erikvanzijst/dotmatrix/media/arduino_tetris.jpg

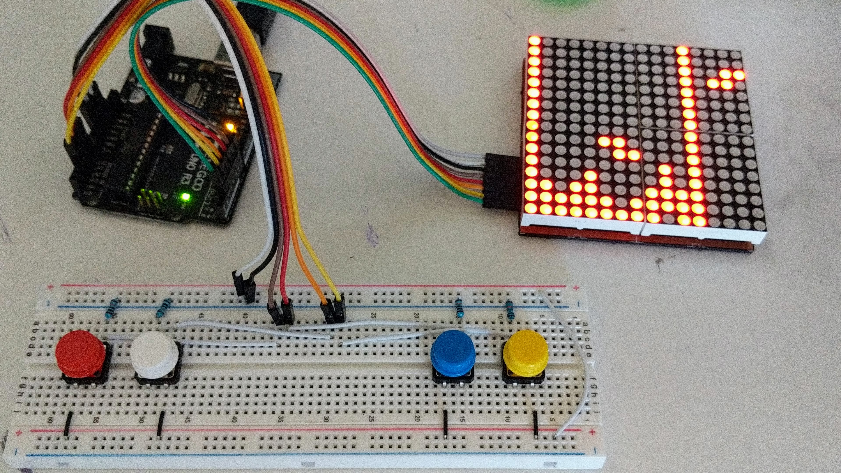
media/arduino_tetris.jpg
