erikvanzijst/dotmatrix/media/board.jpg

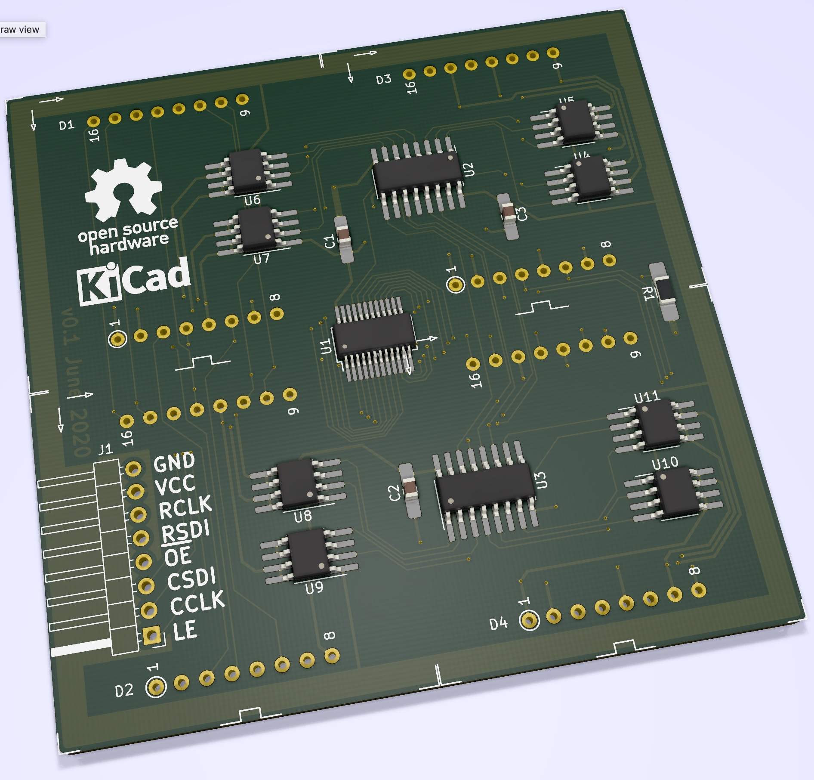
media/board.jpg
