erikvanzijst/dotmatrix/media/logicanalyzer1.jpg

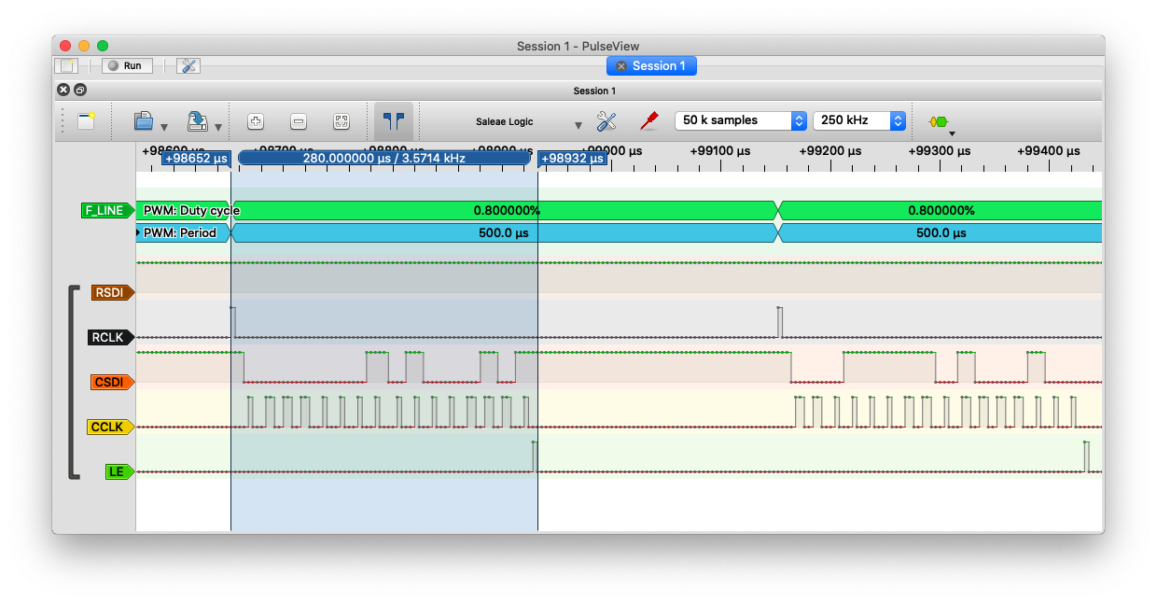
media/logicanalyzer1.jpg
