erikvanzijst/dotmatrix/media/pcb1.jpg

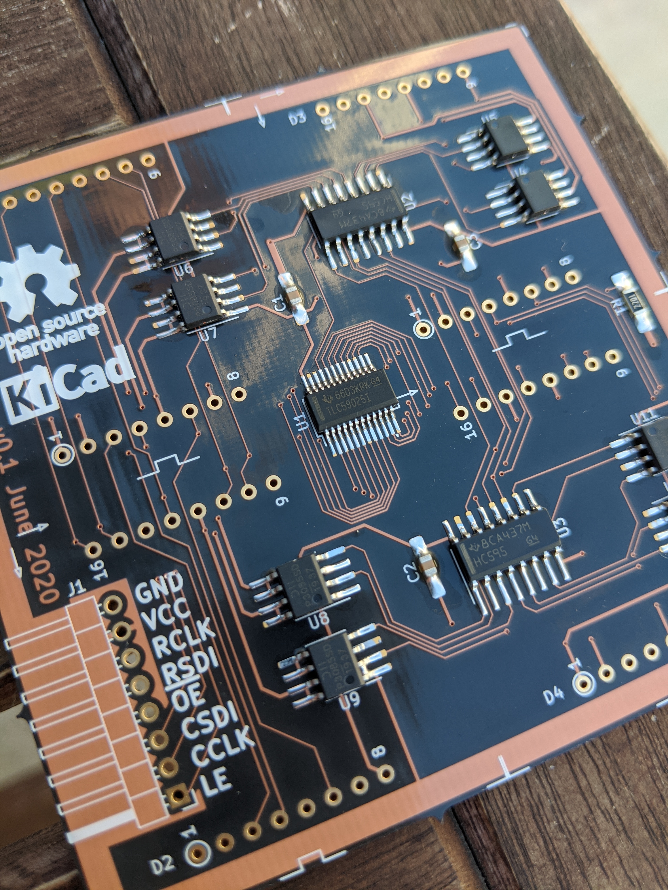
media/pcb1.jpg
