erikvanzijst/dotmatrix/media/pulseview_fastgpio1.jpg

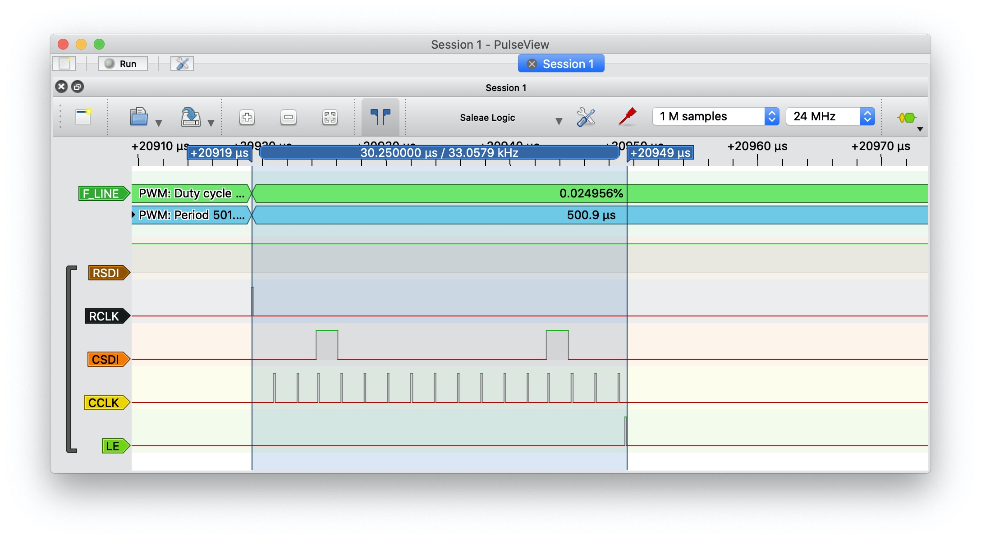
media/pulseview_fastgpio1.jpg
