erikvanzijst/dotmatrix/media/reflow.jpg

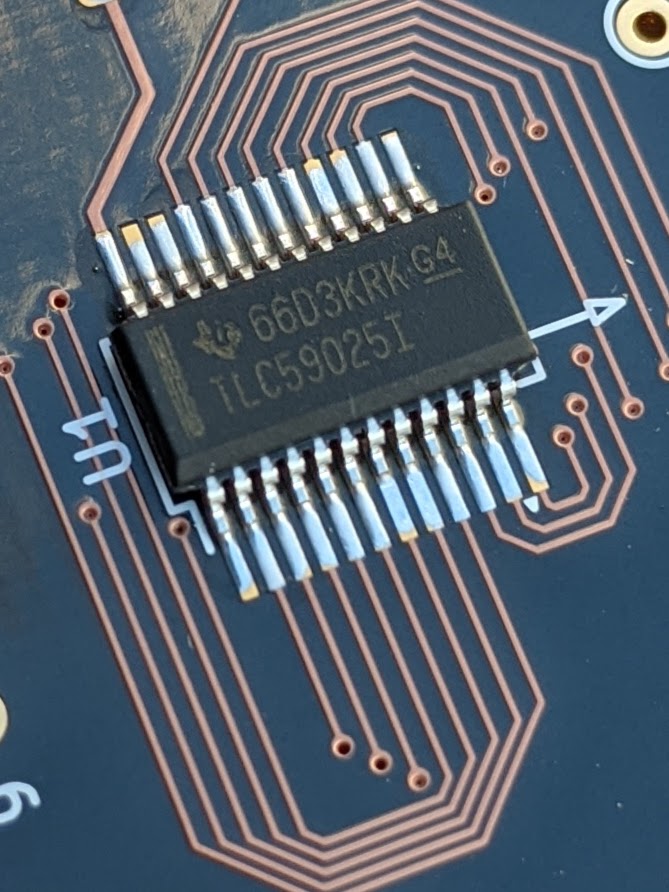
media/reflow.jpg
