erikvanzijst/dotmatrix/media/rendered.jpg

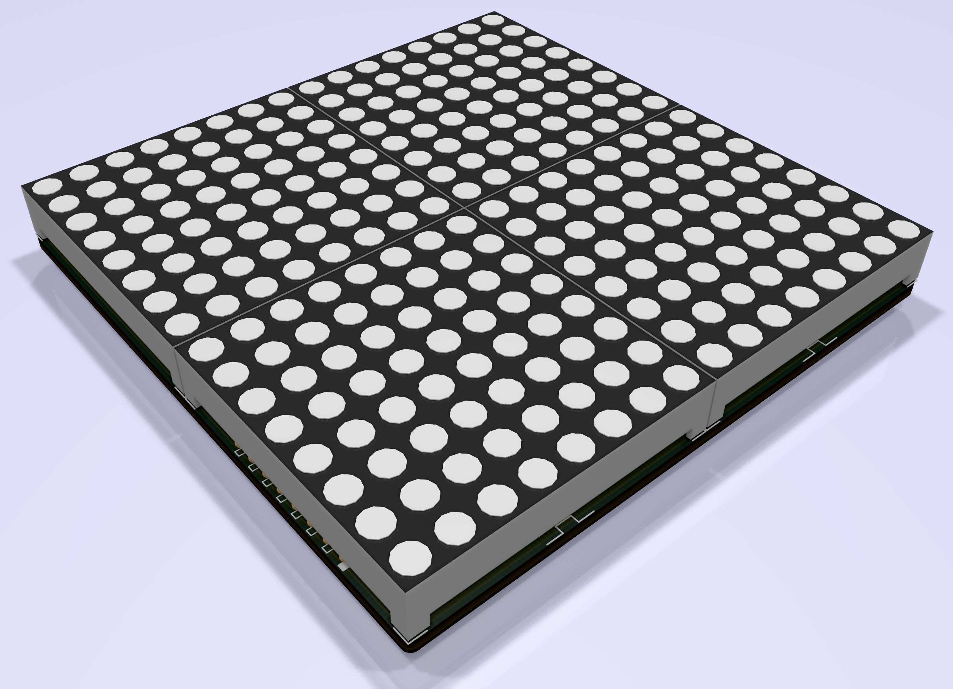
media/rendered.jpg
