erikvanzijst/dotmatrix/media/assembled1.jpg

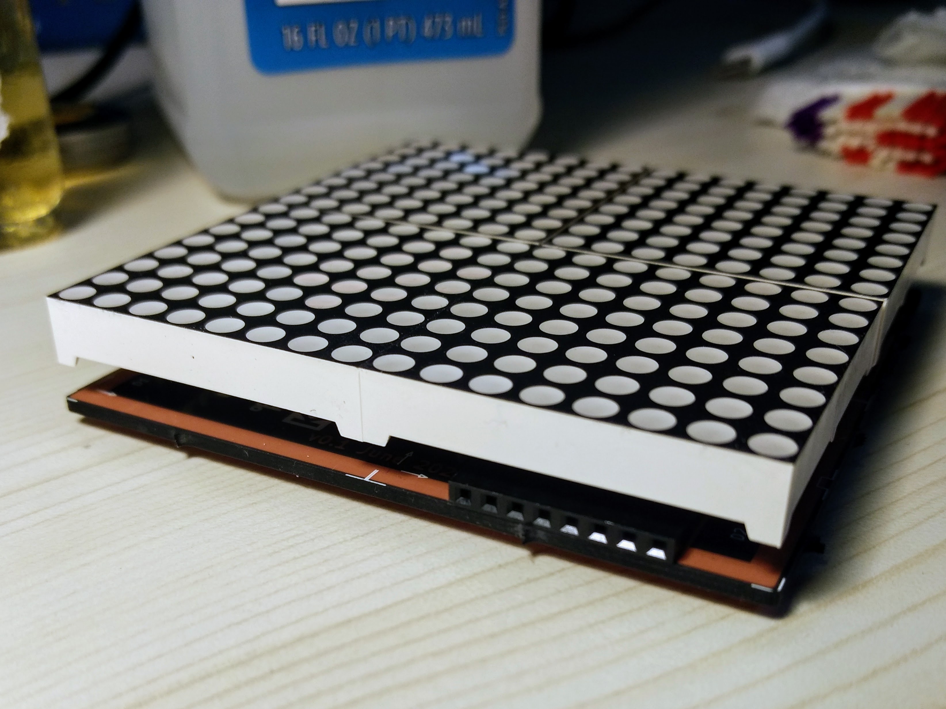
media/assembled1.jpg
